bluesyann/tripico-psu/software/examples/npn_input_characteristics.yaml

comment: BJT NPN curve tracer - base on chA, emmiter on chB and collector on chC
#calibration folder: /media/Bureau/Electronique/iv_calibrations

caracs:
  - name: Input Characteristics
    datafile: test.dat
    init:
        range: 1
        voffset: 5
        sampling: 10
        channels:
          - Name: a
            control: i
            max power: 0.02
            initvalue: 0
          - Name: b
            control: v
            max power: 0.2
            initvalue: 0
          - Name: c
            control: v
            max power: 0.2
            initvalue: 0
    sweep:
        channel: c
        start: 0
        stop: 1
        step: 0.2
        timestep: 1
        sweep:
            channel: a
            start: 1
            stop: 50
            step: 1
            timestep: 0.1
            option: symmetric
    plots:
      - name: Vbe vs. time
        x: t
        xlabel: Time (s)
        y: [va]
        ylabel: Vbe
      - name: Vce vs. time
        x: t
        xlabel: Time (s)
        y: [vc]
        ylabel: Vce
      - name: Ibase vs. Vce
        x: va
        xlabel: Vbe (V)
        y: [ia]
        ylabel: Ibase (mA)
        color: spc
